Lupinixx/SlimeVR-Hyperion-BMI160-PCB/Photos/IMG_20230331_202148.jpg

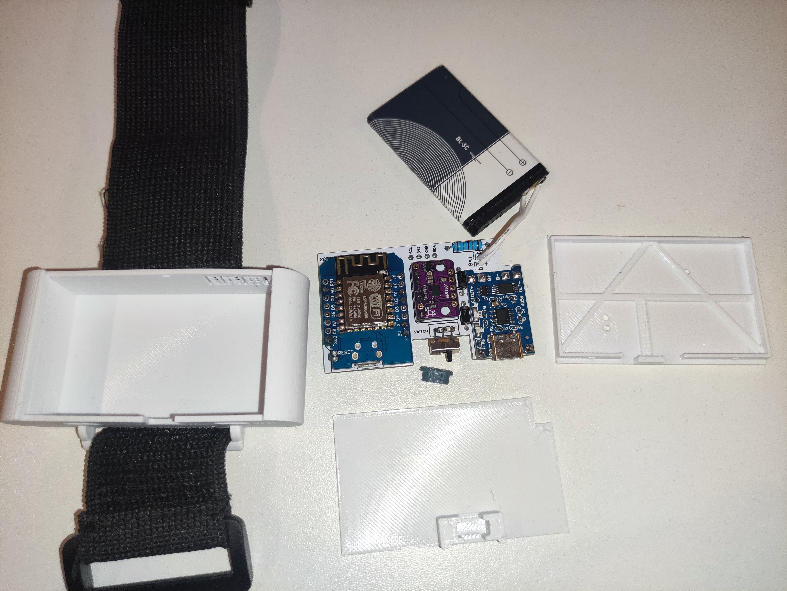
Photos/IMG_20230331_202148.jpg
