Lupinixx/SlimeVR-Hyperion-BMI160-PCB/Photos/IMG_20230331_202250.jpg

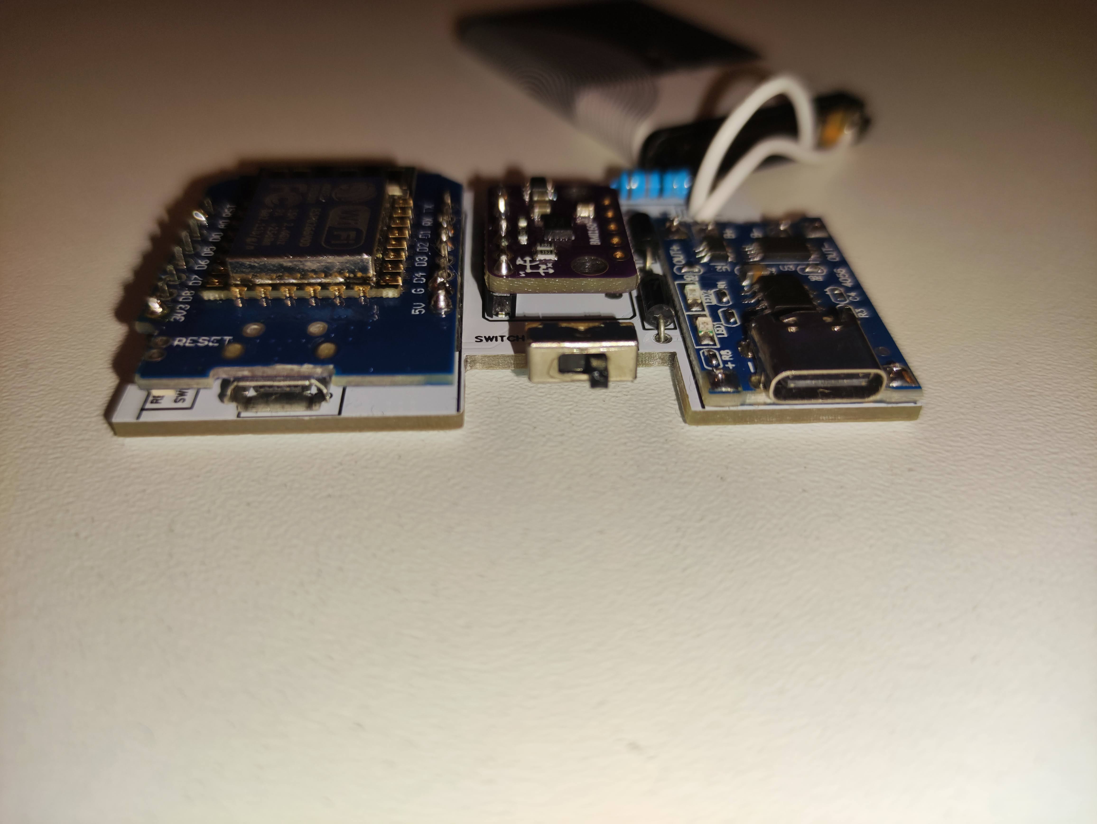
Photos/IMG_20230331_202250.jpg
